vladbalmos/pico-hid-remote/control.h

#define CTRL_CMD_TIMEOUT_MS 60 * 10 * 1000
#define CTRL_DEEP_SLEEP_TIMEOUT_MS 60 * 1000

typedef enum {
    CTRL_EV_MAKE_DISCOVERABLE,
    CTRL_EV_CONNECTED,
    CTRL_EV_DISCONNECTED,
    CTRL_EV_REQUEST_TOGGLE_PLAY,
    CTRL_EV_REQUEST_VOL_UP,
    CTRL_EV_REQUEST_VOL_DOWN
} ctrl_ev_type_t;

typedef struct {
    ctrl_ev_type_t type;
    void *data;
} ctrl_ev_t;

ctrl_ev_t ctrl_make_event(ctrl_ev_type_t ev_type, void *data);

void ctrl_init(queue_t *write_queue, queue_t *read_queue);
void ctrl_deinit();
void ctrl_process_queue();
void ctrl_make_discoverable(uint8_t state);
void ctrl_toggle_play_pause();
void ctrl_vol_up();
void ctrl_vol_down();
