vladbalmos/pico-hid-remote/debug.h

#include <stdio.h>

#ifdef DEBUG_MODE
    #define DEBUG(...) printf(__VA_ARGS__);
#else
    #define DEBUG(...) do {} while (0)
#endif

inline bool debug_mode() {
#ifdef DEBUG_MODE
    return true;
#else
    return false;
#endif
}

void hci_event_code_str(uint8_t event_code, char* output);
